samowitsch/custom-arduino-rtc-temperature-humidity/research/1329269952131.png

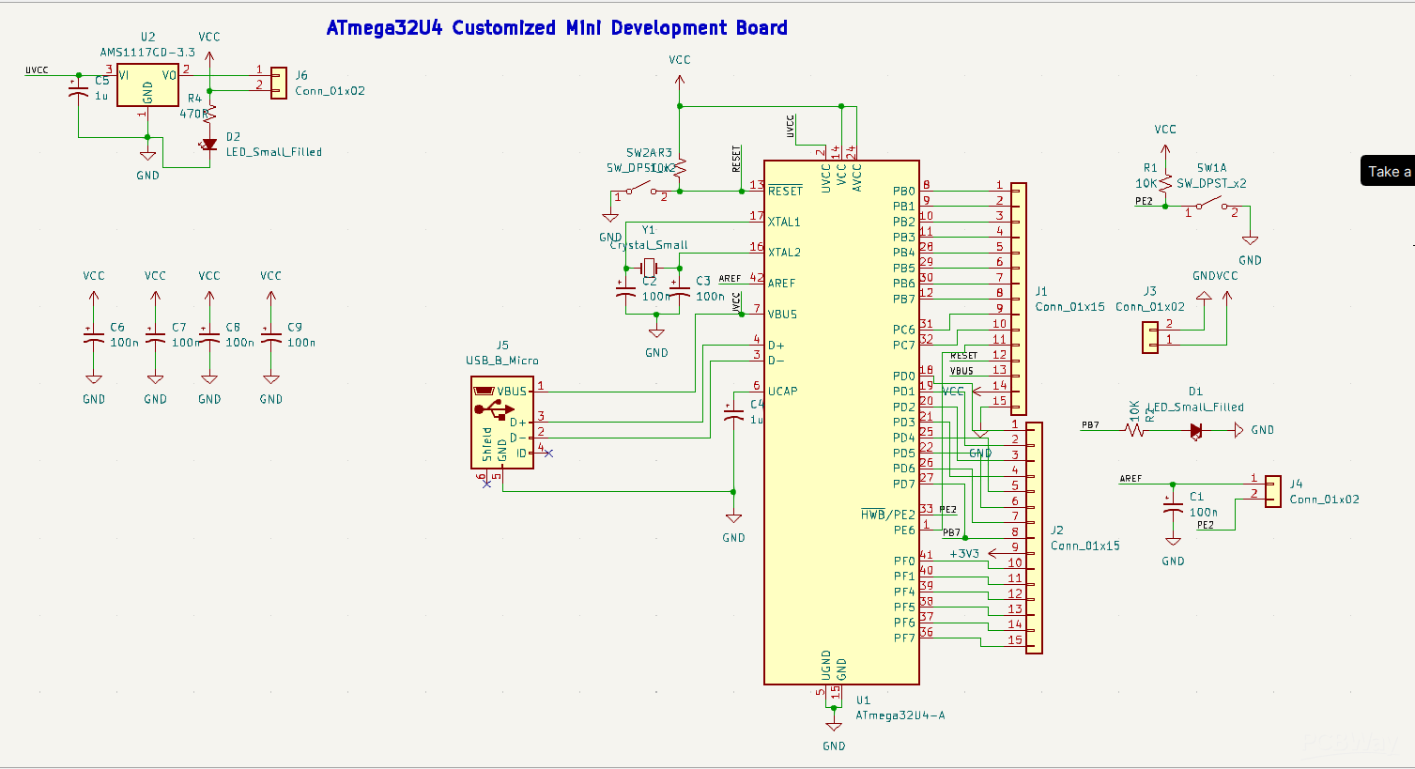
research/1329269952131.png
