samowitsch/custom-arduino-rtc-temperature-humidity/research/arduino-compatible-with-onboard-rtc.jpeg

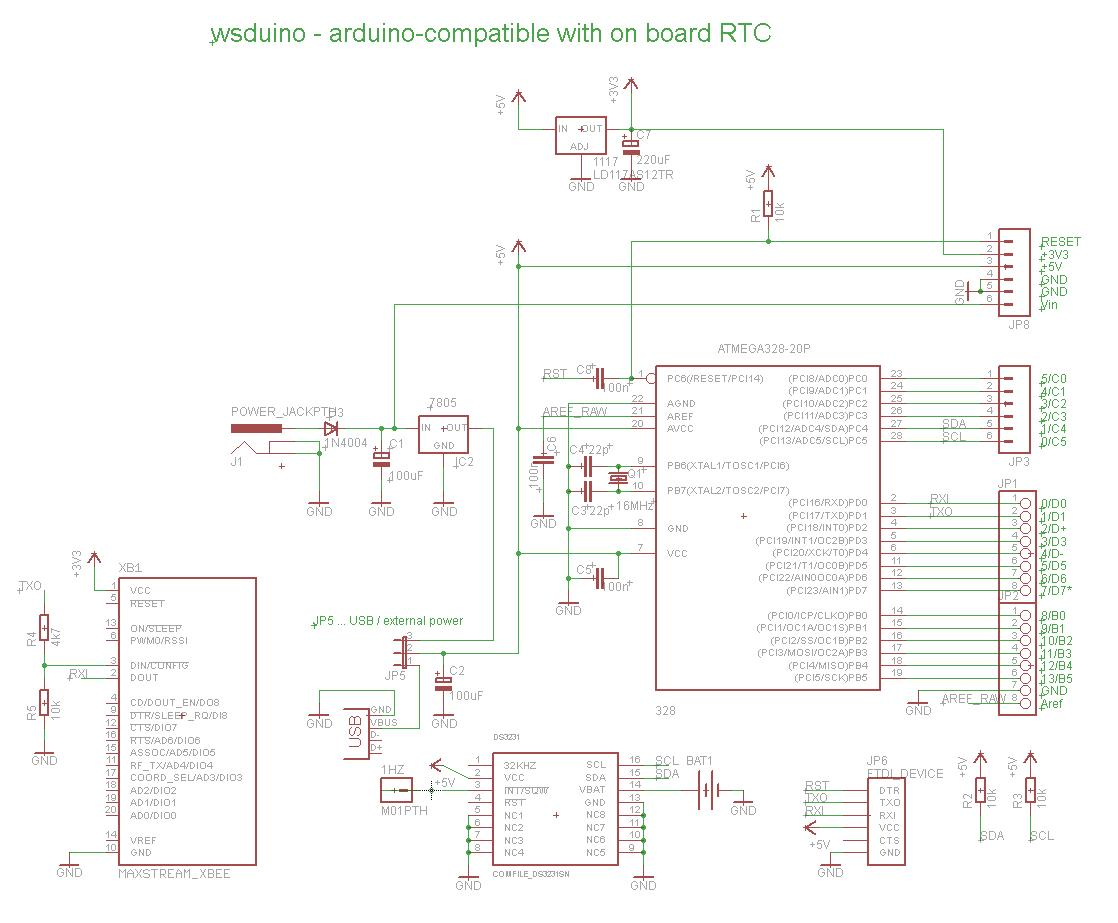
research/arduino-compatible-with-onboard-rtc.jpeg
