samowitsch/custom-arduino-rtc-temperature-humidity/research/arduino-ds3231-sd-card.png

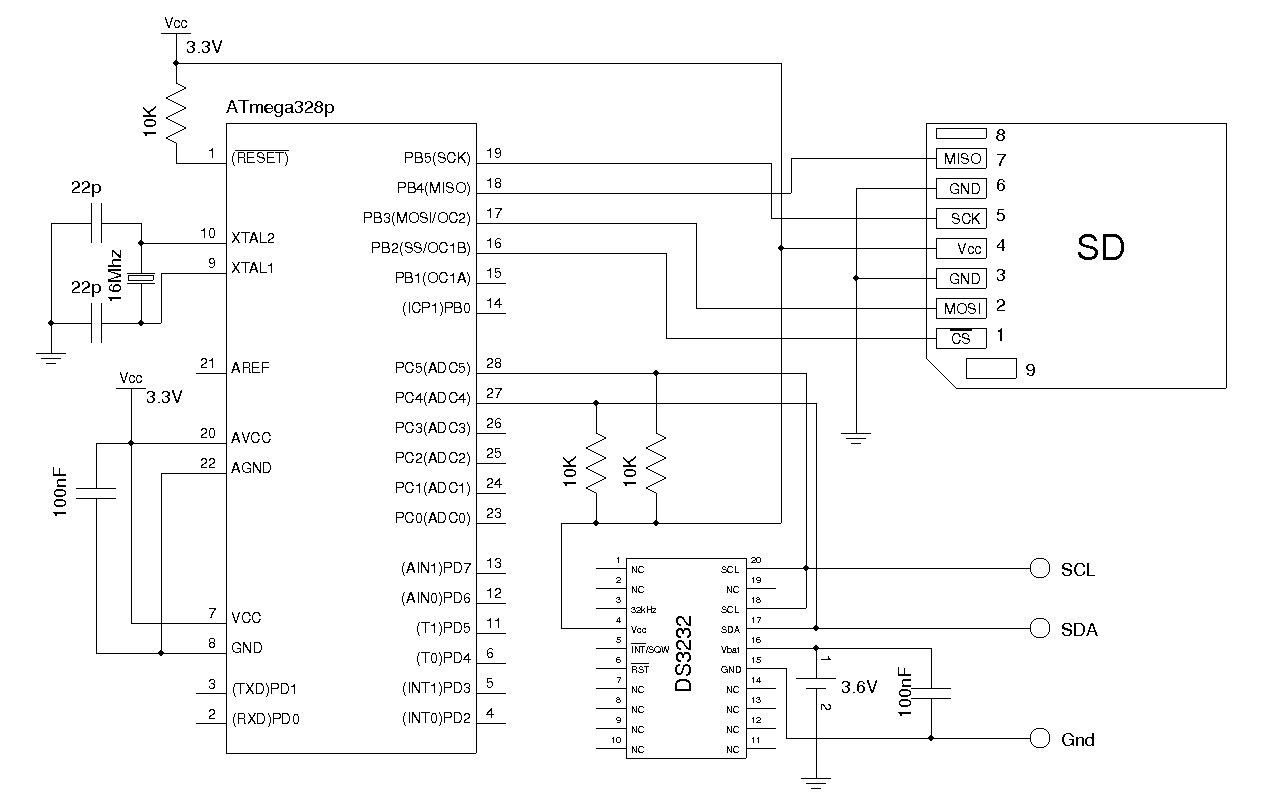
research/arduino-ds3231-sd-card.png
