samowitsch/custom-arduino-rtc-temperature-humidity/research/controlunitpic18f4550.png

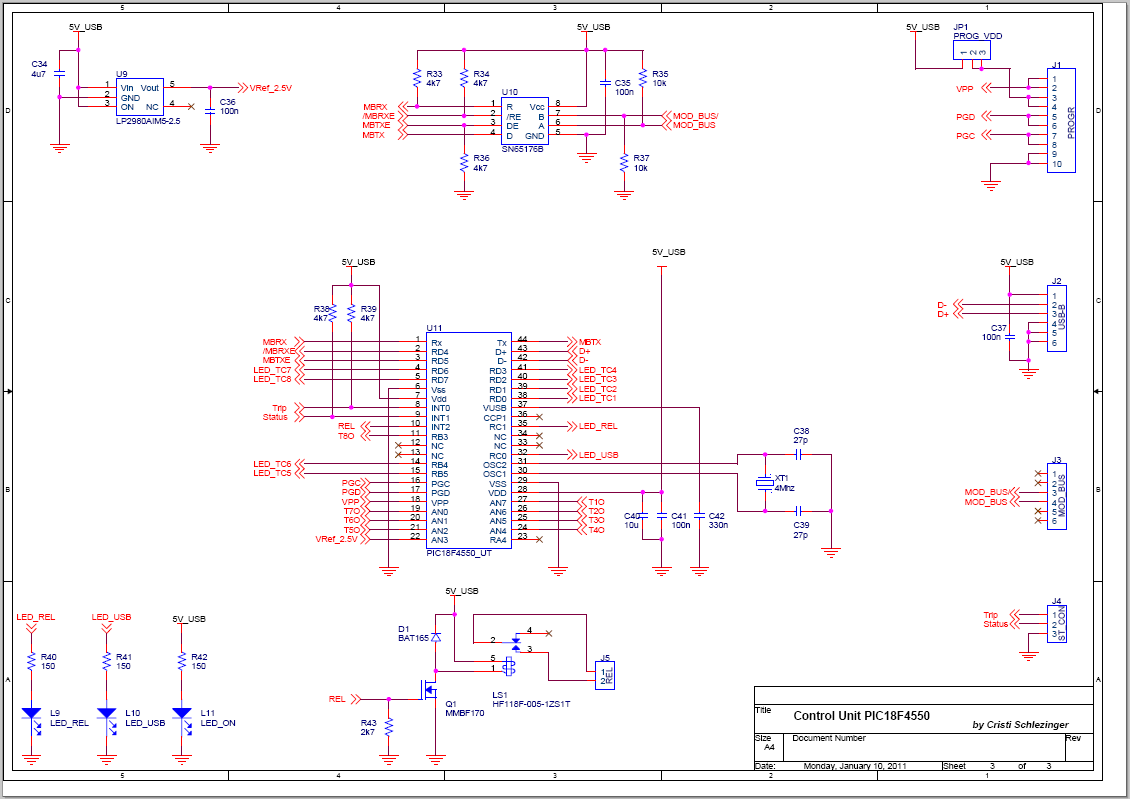
research/controlunitpic18f4550.png
