samowitsch/custom-arduino-rtc-temperature-humidity/research/Download.gif

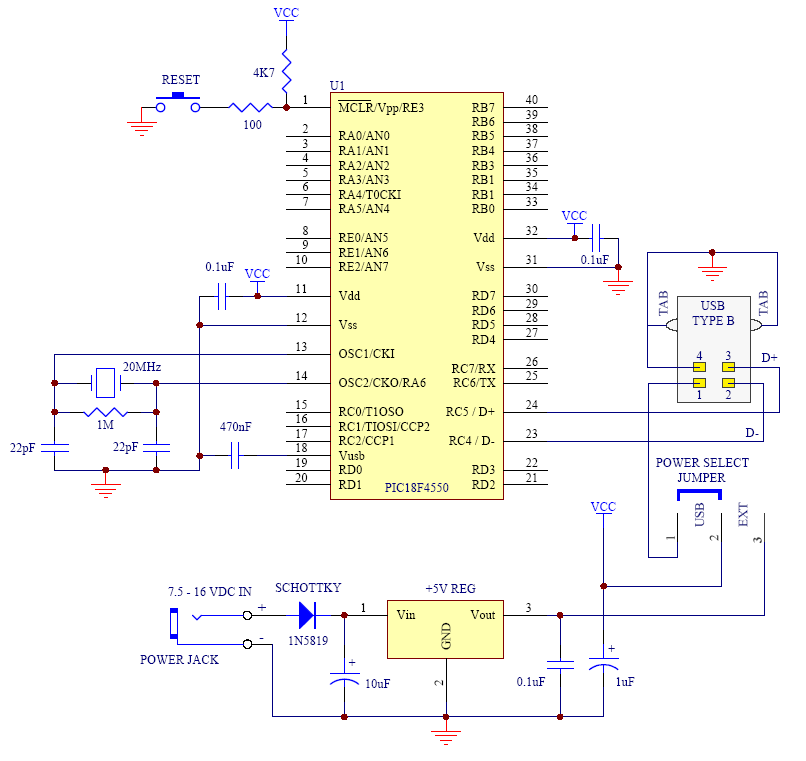
research/Download.gif
