samowitsch/custom-arduino-rtc-temperature-humidity/research/a-star-32u4-prime-lv-ac03e-schematic.pdf

# A-Star 32U4 Prime LV

# Schematic diagram

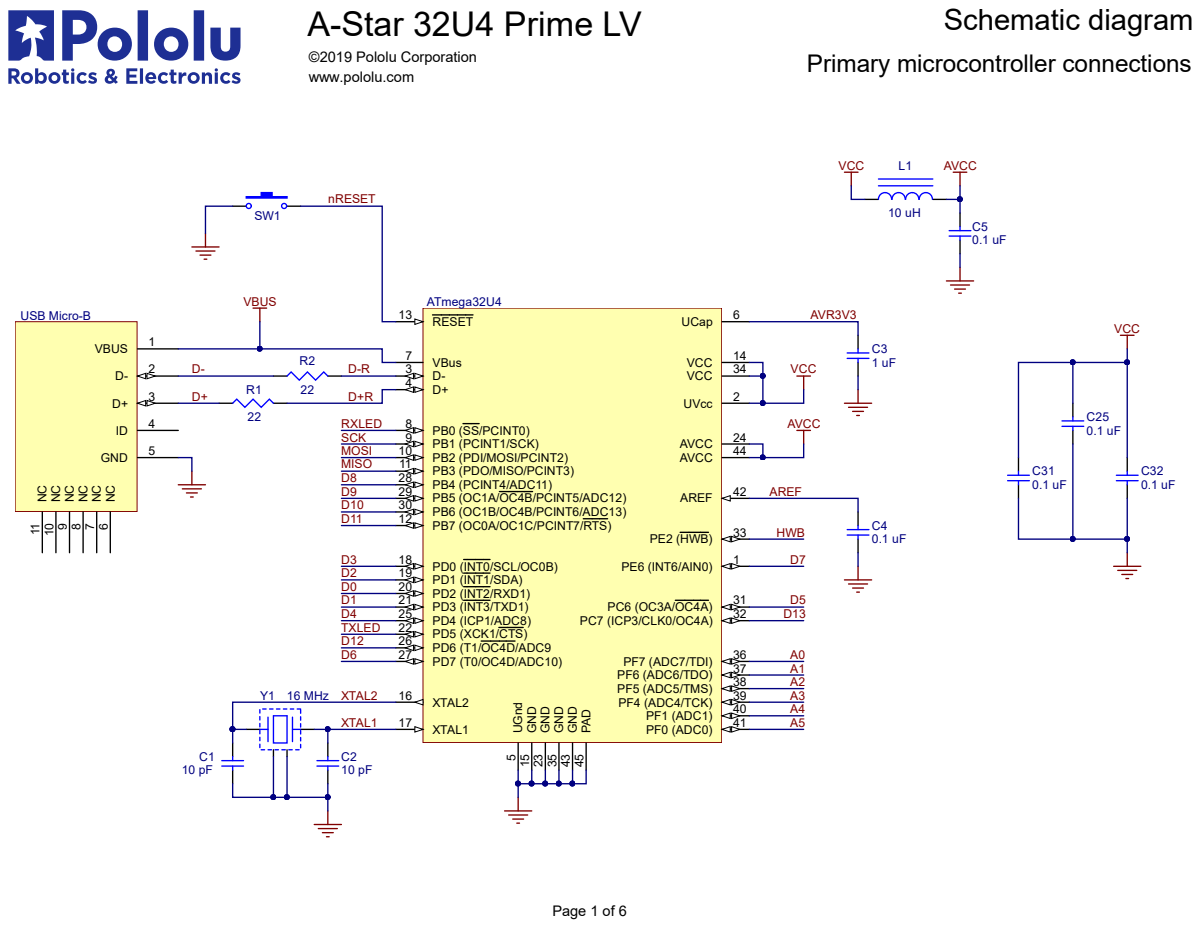
[picture p21: page 1]

# A-Star 32U4 Prime LV

# External connections

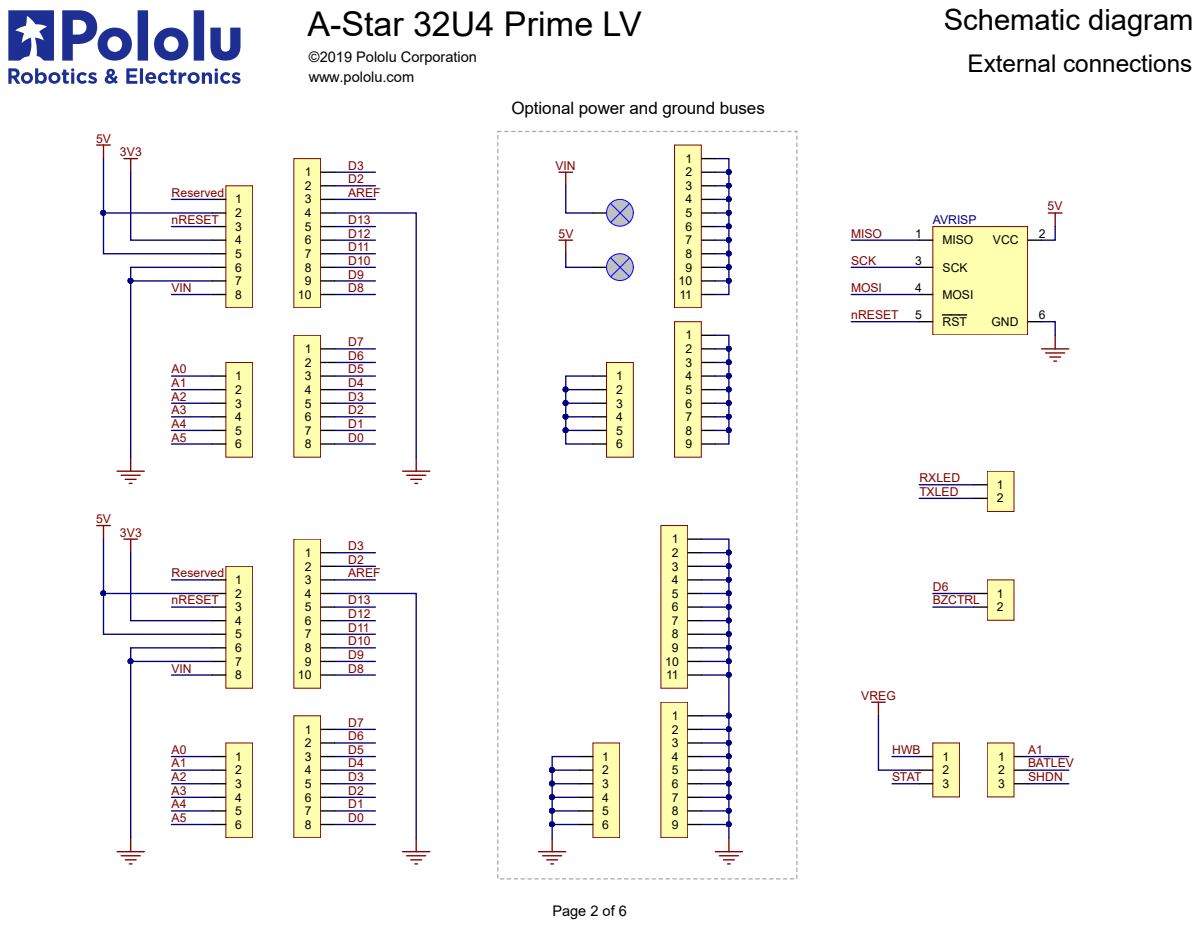
[picture p22: page 2]

Optional power and ground buses

# A-Star 32U4 Prime LV

# On-board hardware

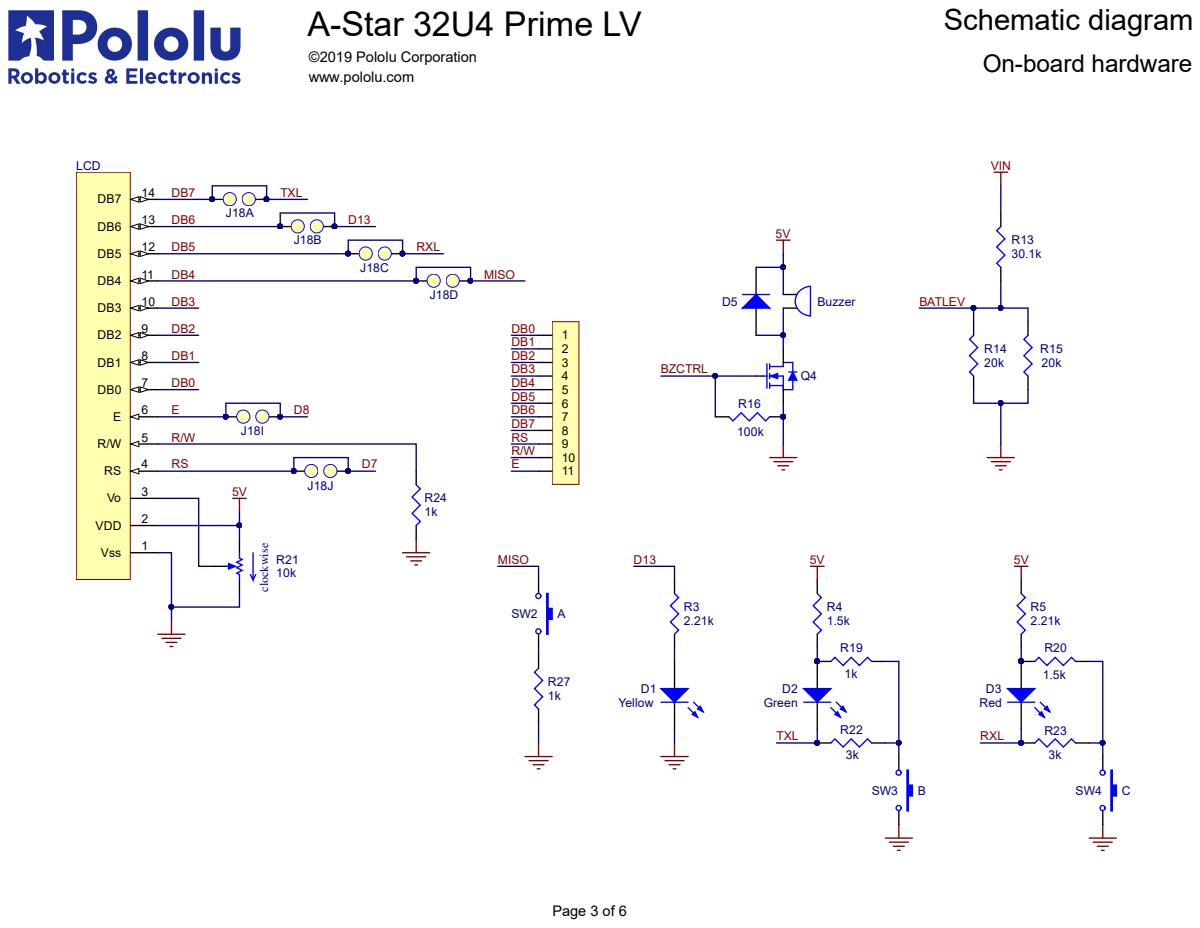
[picture p23: page 3]

# A-Star 32U4 Prime LV

# Power multiplexing

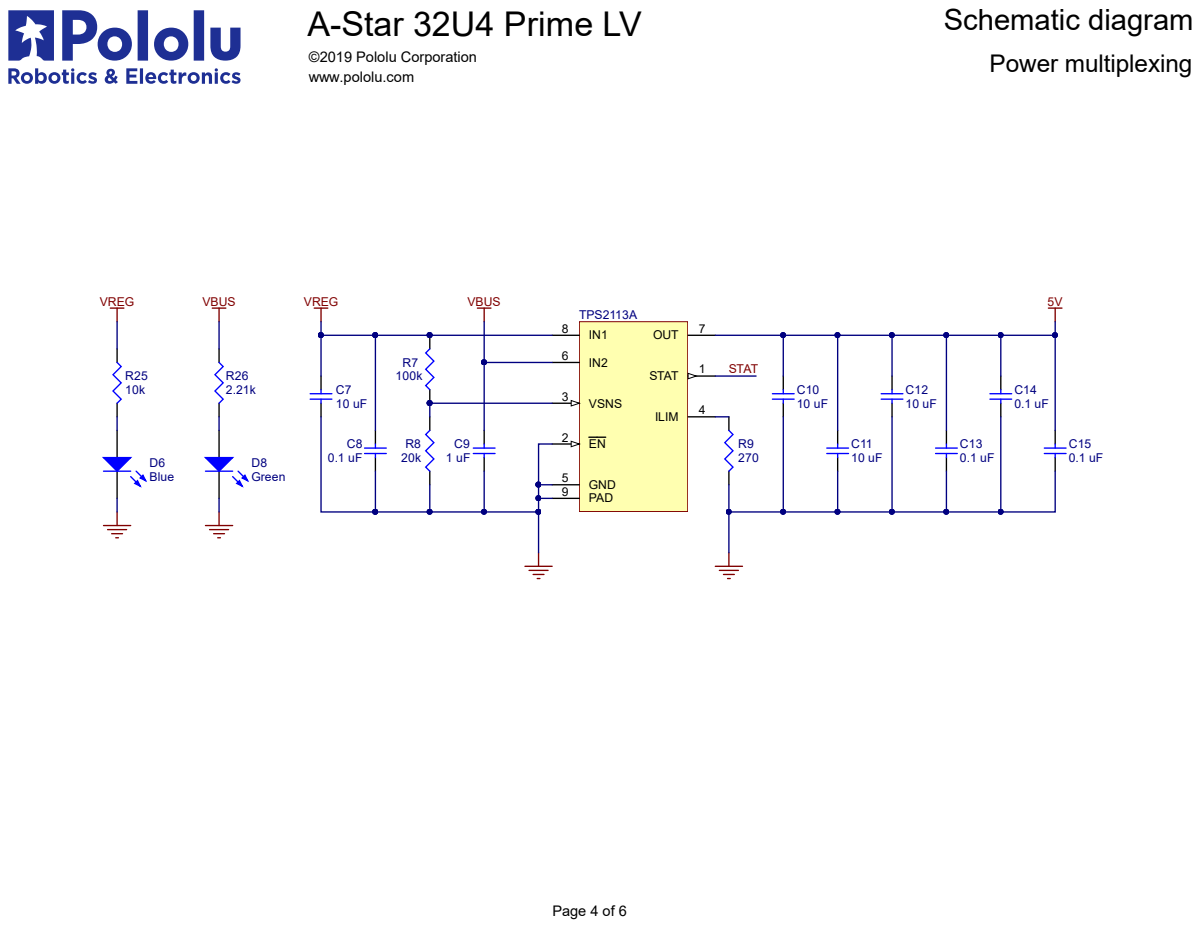
[picture p24: page 4]

# A-Star 32U4 Prime LV

# Regulators and power connectors

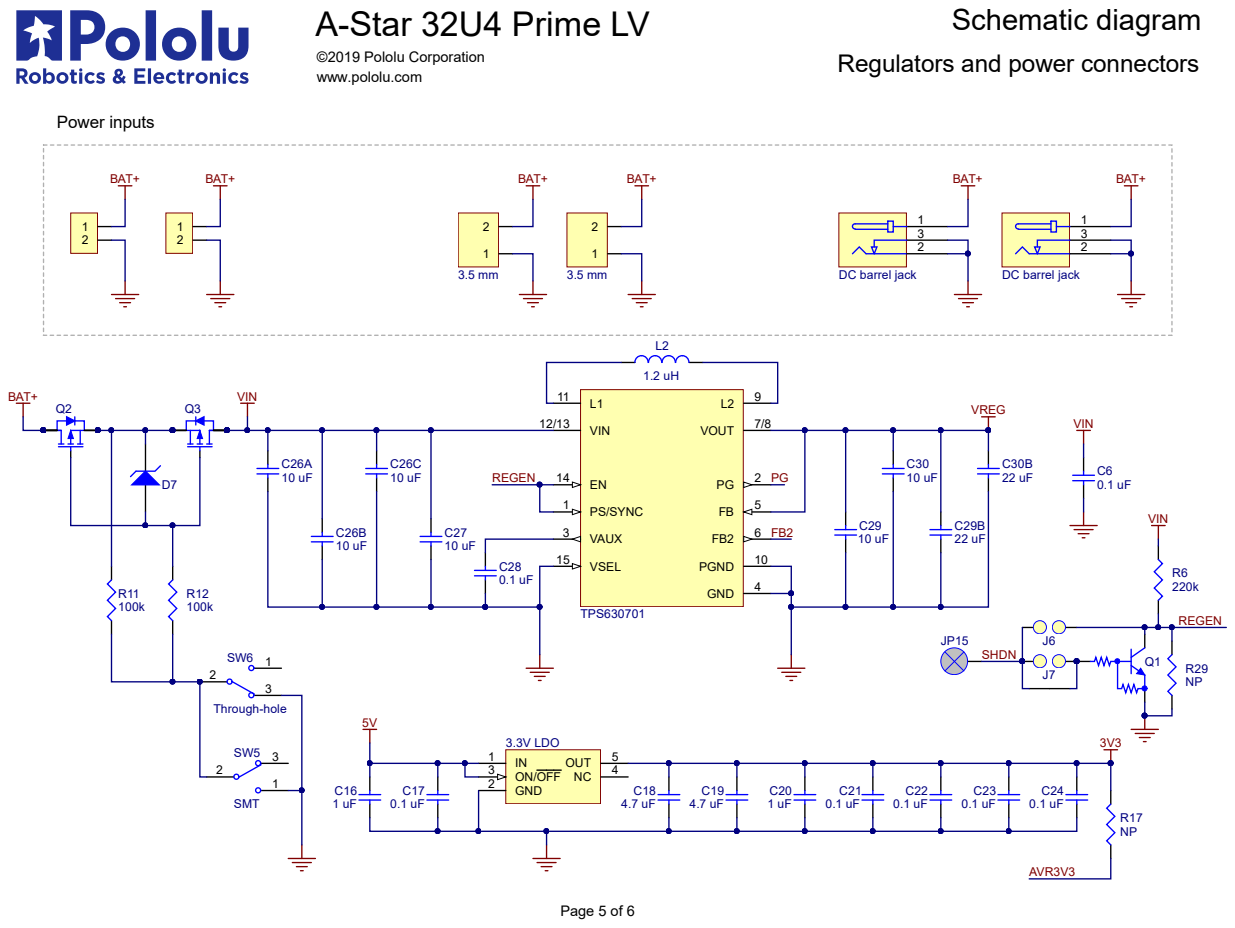
[picture p25: page 5]

# A-Star 32U4 Prime LV

# microSD hardware

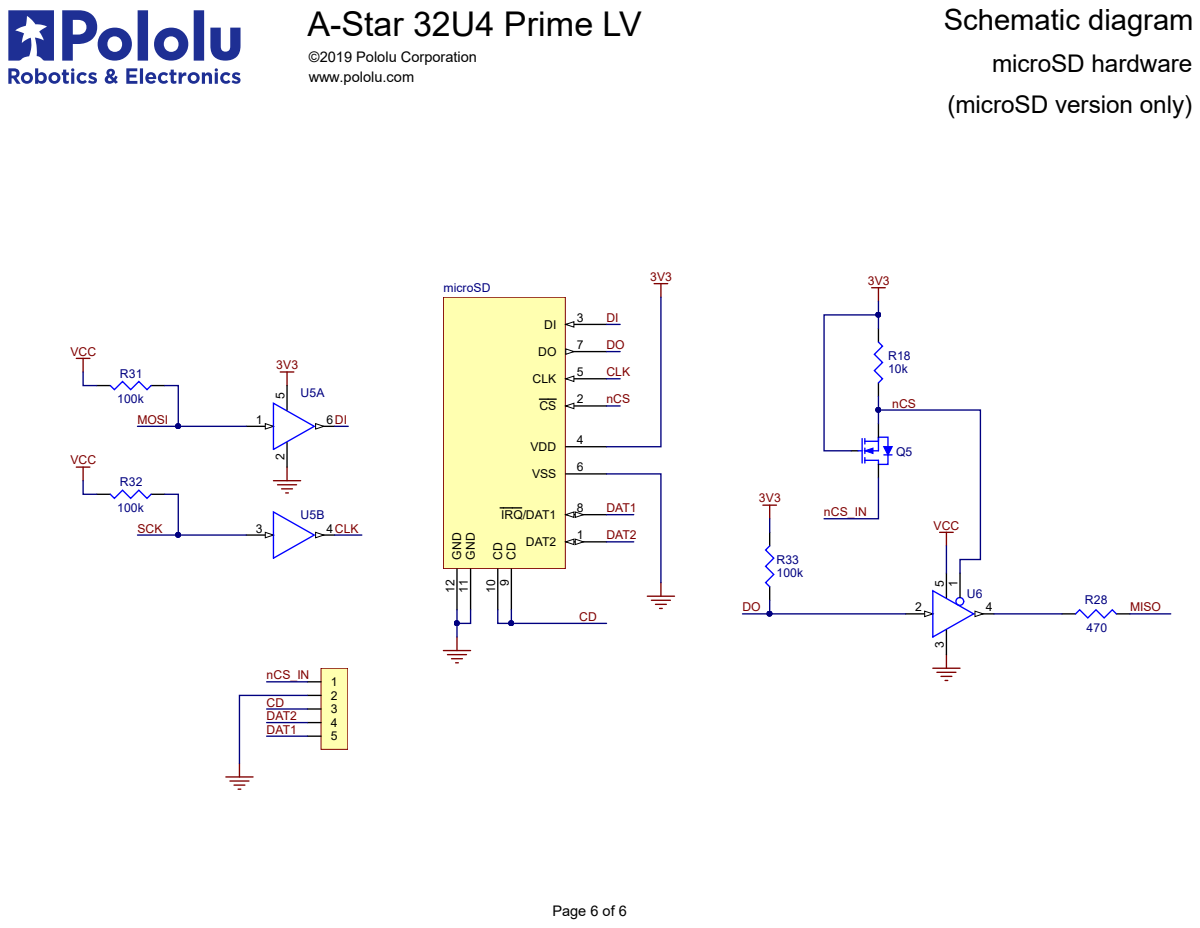
[picture p26: page 6]
