samowitsch/custom-arduino-rtc-temperature-humidity/research/a-star_32u4_prime_sv_schematic_diagram.pdf

# A-Star 32U4 Prime SV

# Schematic diagram

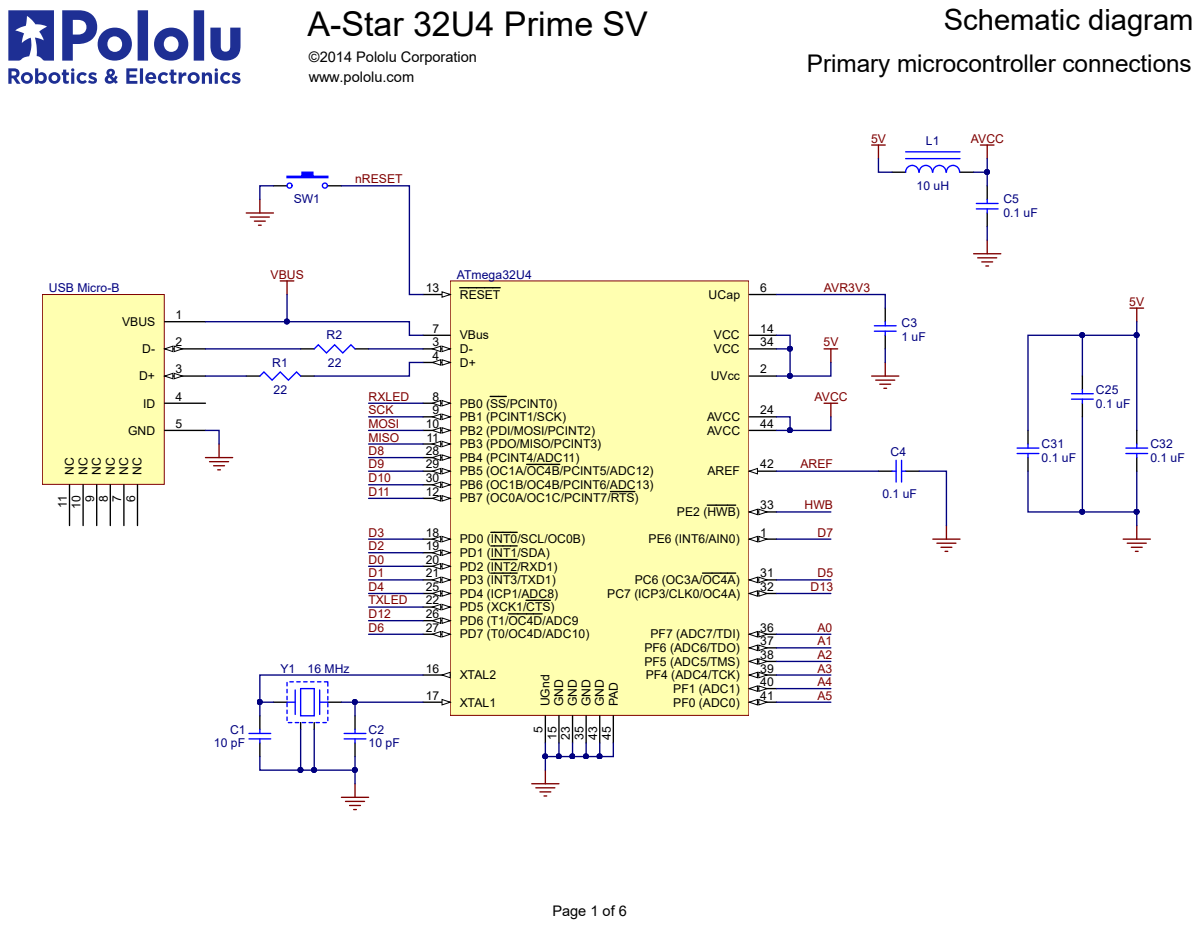
[picture p27: page 1]

# A-Star 32U4 Prime SV

# External connections

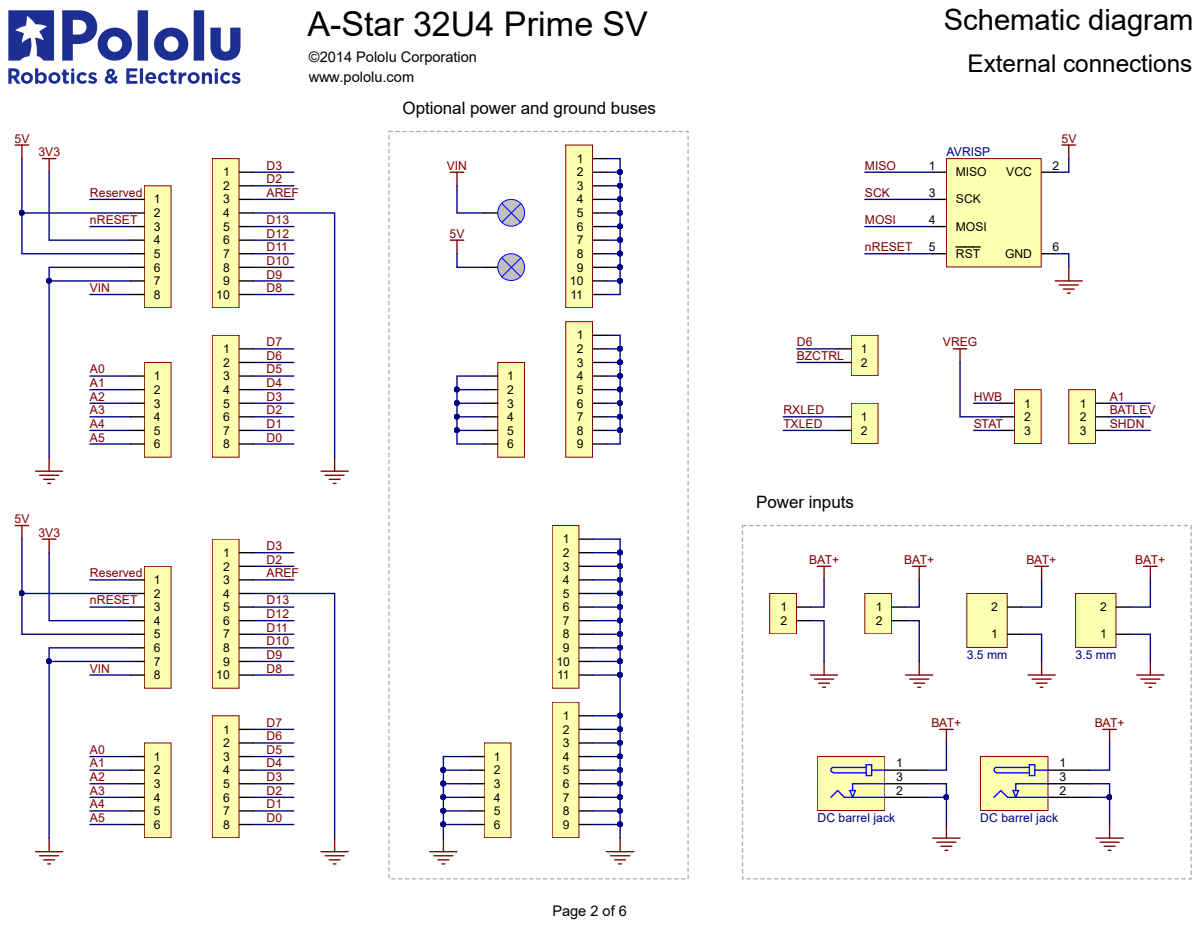
[picture p28: page 2]

Optional power and ground buses

# A-Star 32U4 Prime SV

# On-board hardware

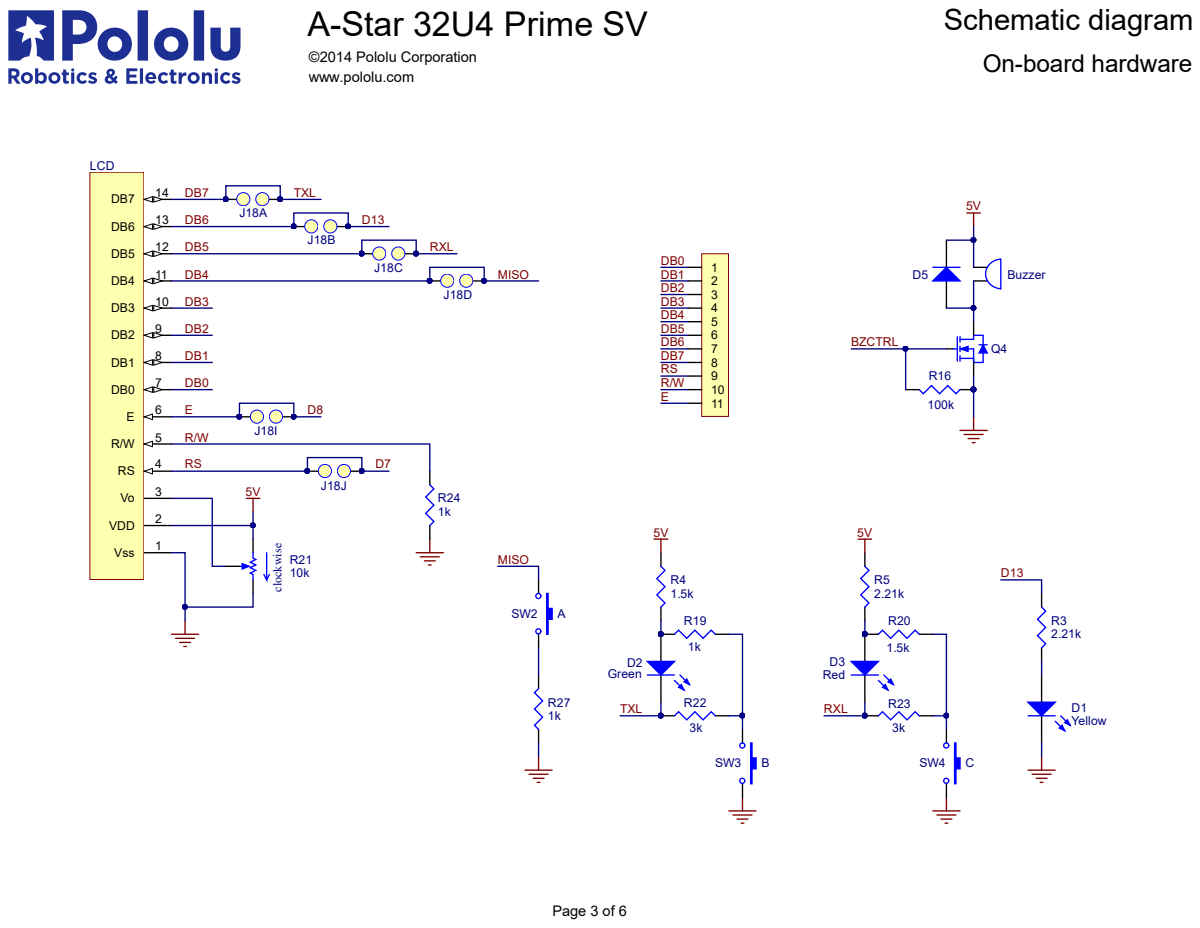
[picture p29: page 3]

# A-Star 32U4 Prime SV

# Power multiplexing

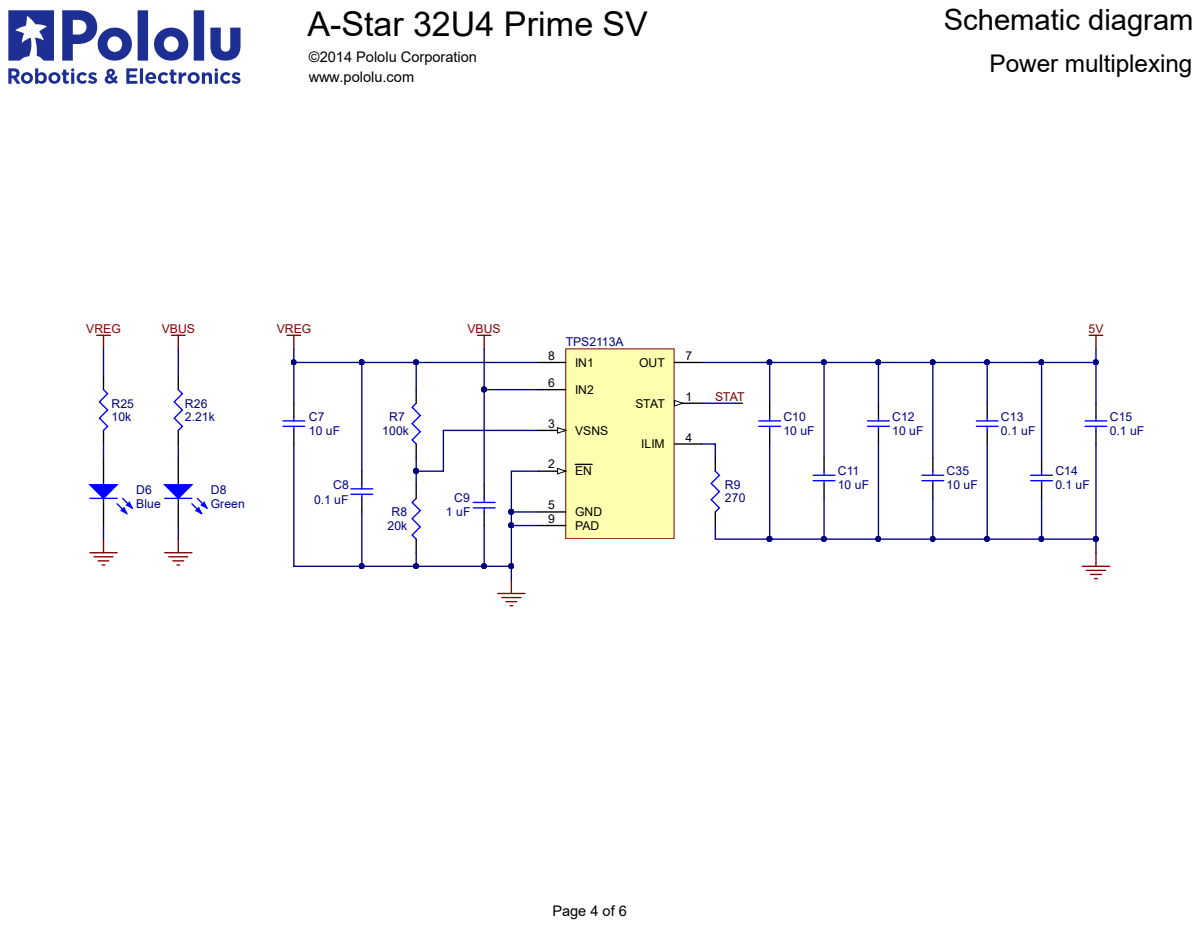
[picture p30: page 4]

# A-Star 32U4 Prime SV

# Regulators and power connectors

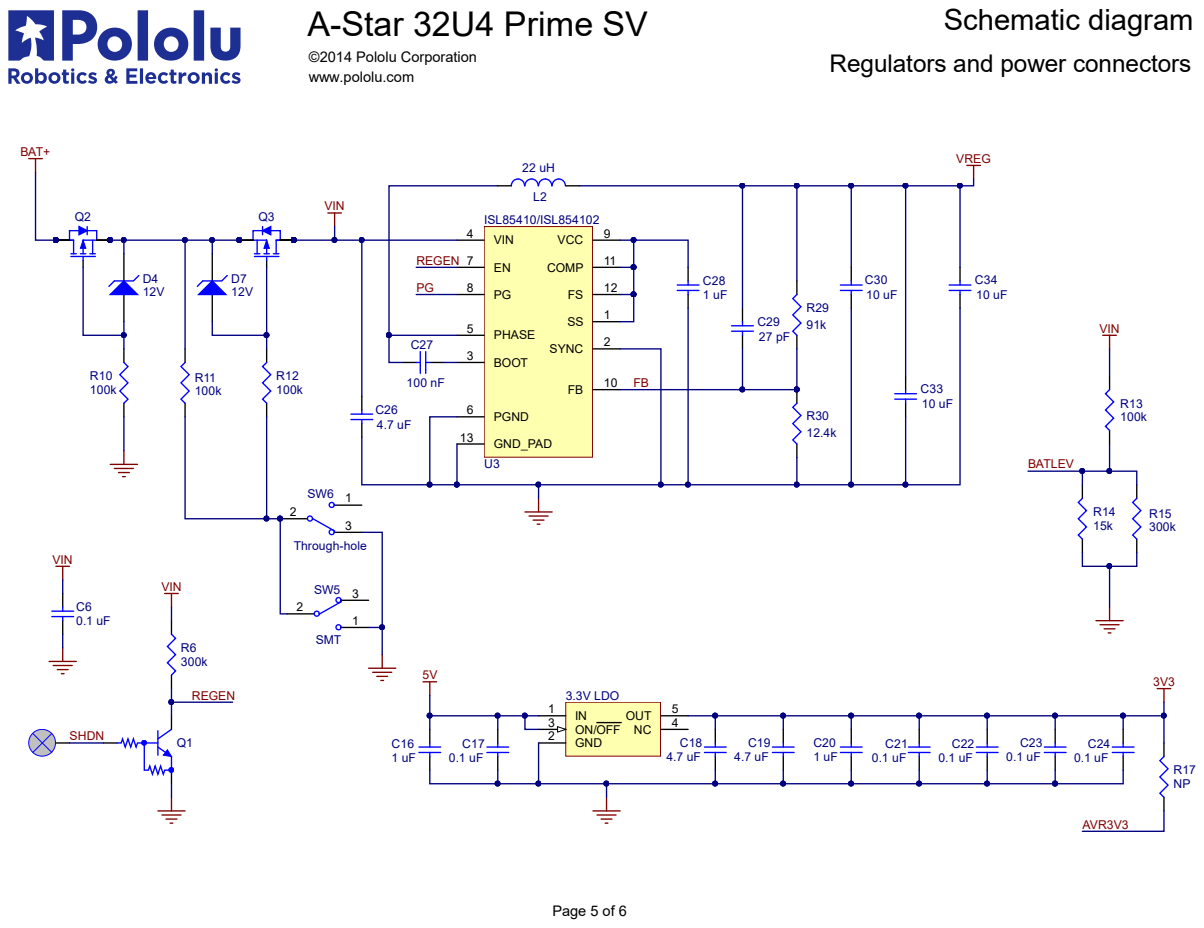
[picture p31: page 5]

# A-Star 32U4 Prime SV

# microSD hardware

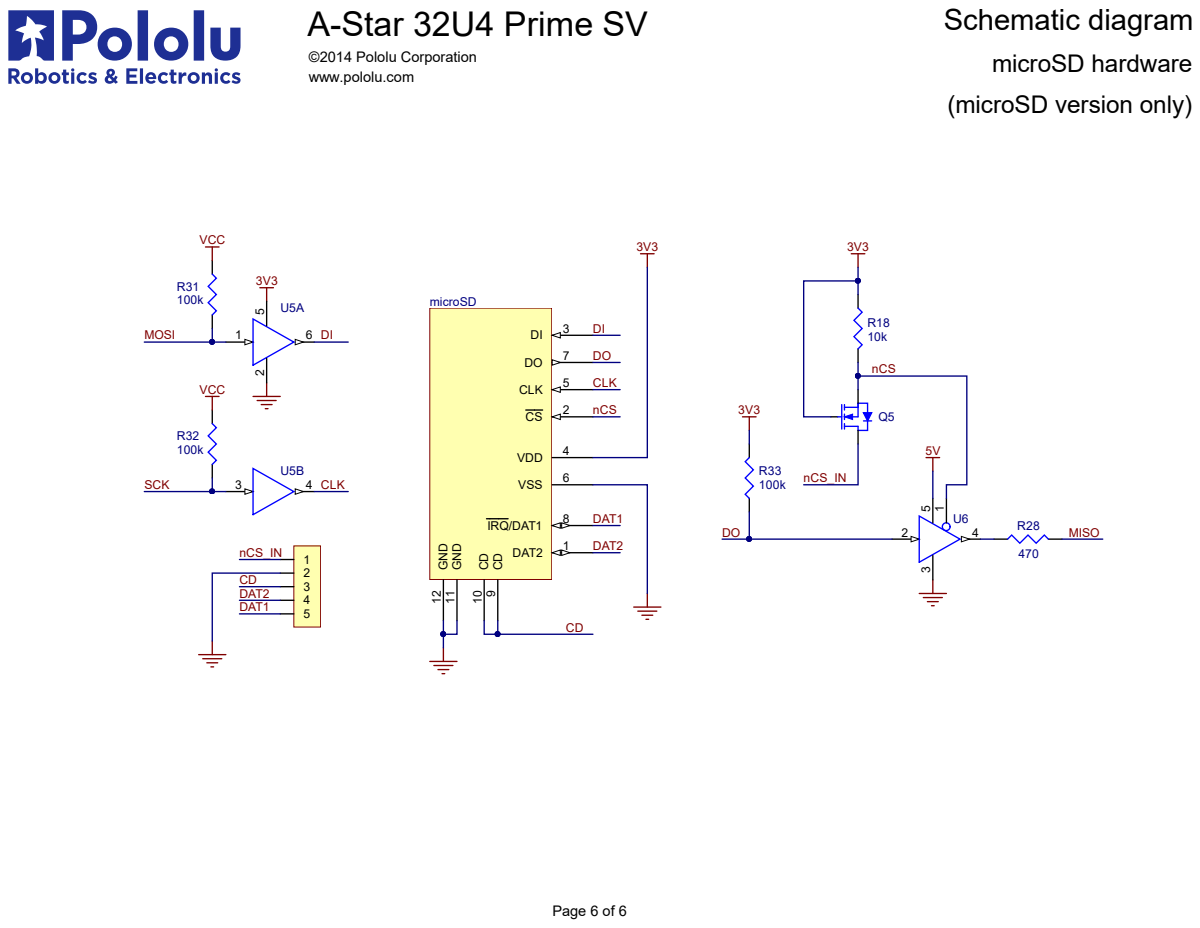
[picture p32: page 6]
