samowitsch/custom-arduino-rtc-temperature-humidity/research/Arduino-Fio_v31a.pdf

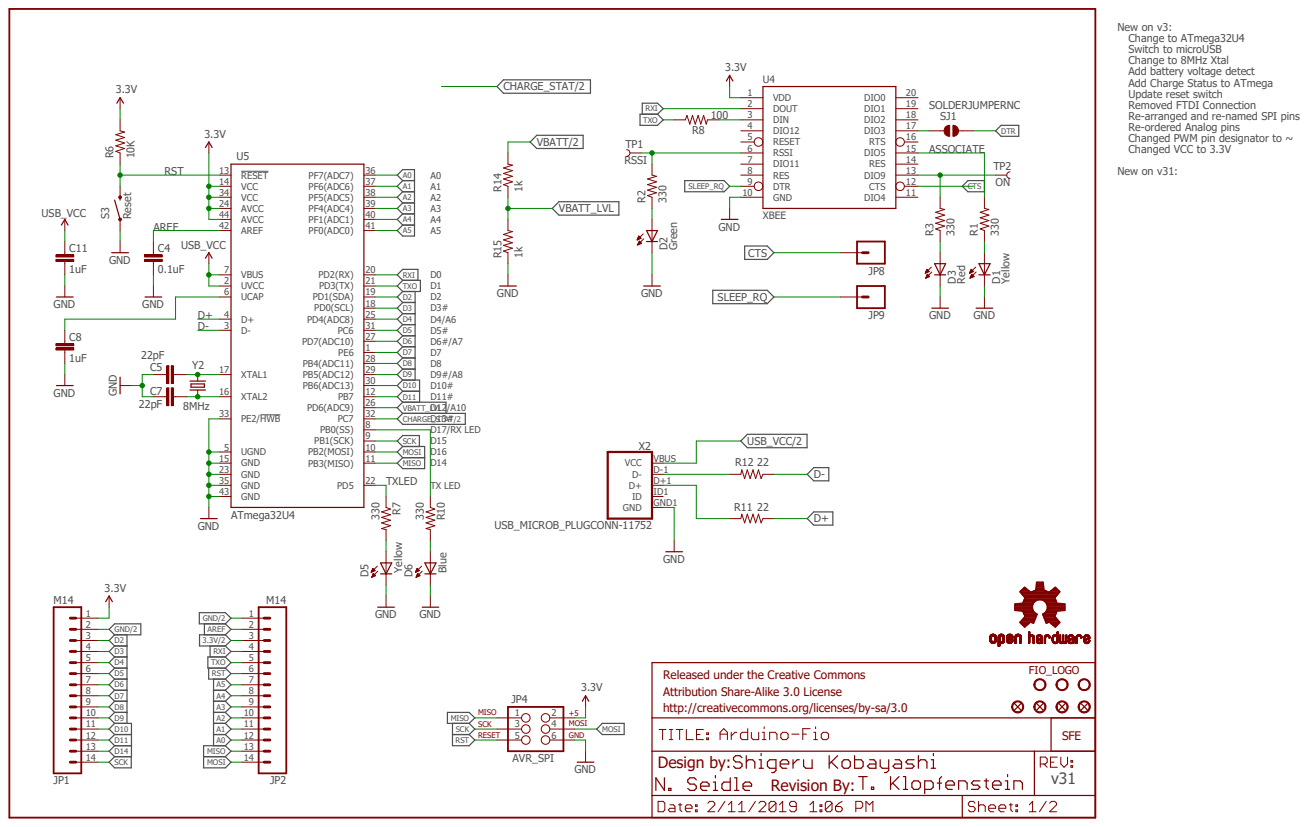
[picture p33: page 1]

New on v3:
Change to ATmega32U4
Switch to microUSB
Change to 8MHz Xtal
Add battery voltage detect
Add Charge Status to ATmega
Update reset switch
Removed FTDI Connection
Re-arranged and re-named SPI pins
Re-ordered Analog pins
Changed PWM pin designator to ~
Changed VCC to 3.3V
New on v31:

Released under the Creative Commons
Attribution Share-Alike 3.0 License
http://creativecommons.org/licenses/by-sa/3.0

## Cut this jumper if powering the board with more than 5.5V

## Power Switch

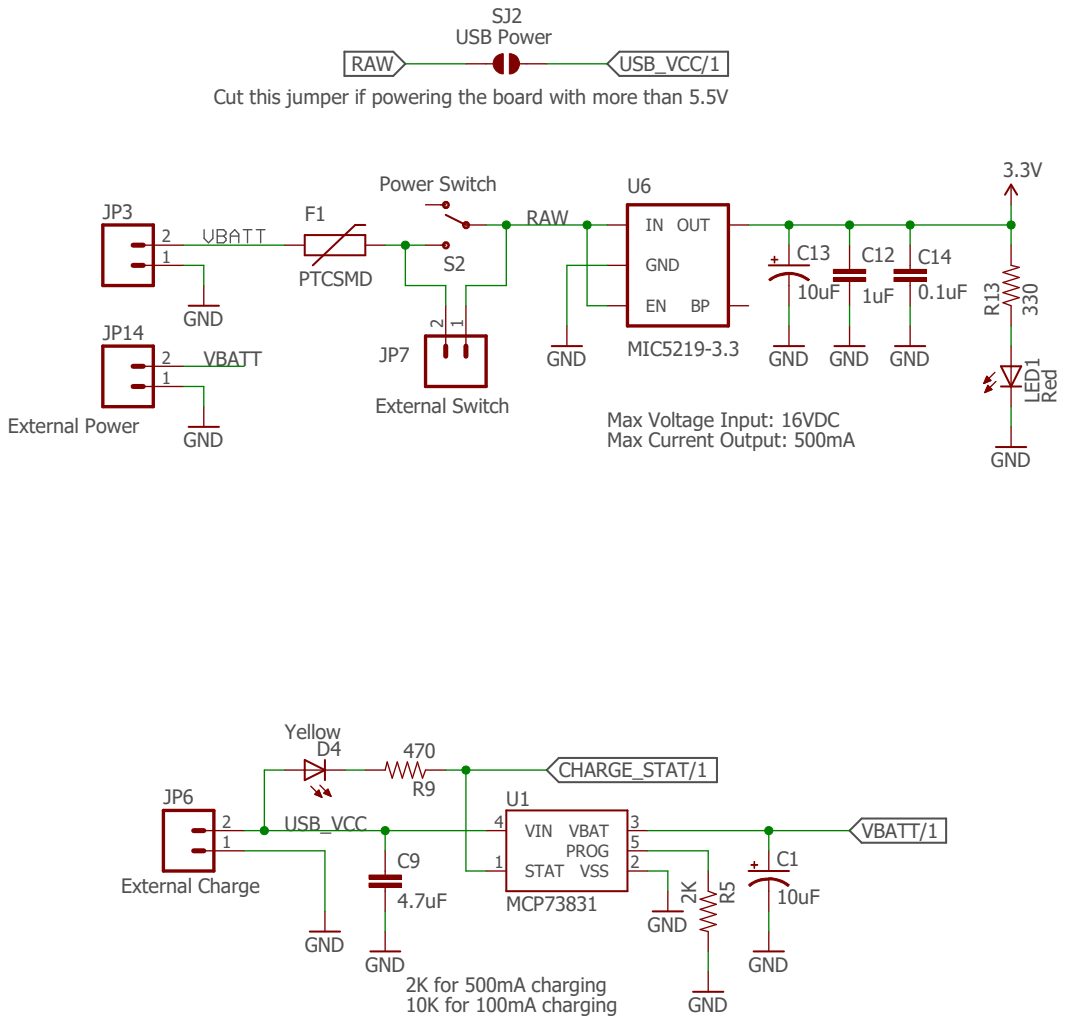
[picture p34: page 2]
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
